2nd-junkey/coinmag/roll/5/key.scad

include <args.scad>

key_width = case_hole_radius;

key_radius = chember_radius;

// half circle
difference(){
    cylinder(h = key_thickness, r = key_radius, center = false);
    translate([0, key_radius/2, 0]){
        cube([key_radius*2, key_radius, key_thickness*2], center = true);
    }
}
// inserting
intersection(){
    cylinder(h = key_thickness, r = key_radius, center = false);
    translate([0, 0, key_thickness]){
        cube([key_width*2, key_width*2, key_thickness*2], center = true);
    }
}
